SlightlyCyborg/StructureSensorBot/hardware/scad/alignment_cube.scad

cube([4.5,6.6,4.5]);
