SlightlyCyborg/StructureSensorBot/hardware/scad/test_peg.scad

translate([0,0,3.5])
cube([4.7,6.7,7], center=true);

translate([0,0,-3])
cylinder(r=7, 3);
